mtfurlan/elite-dangerous-control-panel/src/config.cpp

#include "config.h"
bool Config::generateOutput(uint16_t* output, uint16_t button, hid_incoming_data_t* hid)
{
    return false;
}

void Config::setLED(uint16_t* leds, hid_incoming_data_t* hid)
{
    return;
}

int Config::init(void)
{
    return 0;
}
