mtfurlan/elite-dangerous-control-panel/src/config_led.cpp

#include "config_led.h"

void ConfigLED::setLED(uint16_t* leds, hid_incoming_data_t* hid)
{
    if (this->LEDPin) {
        bool input_state = this->GetState(hid);
        CFG_SET_BIT_VAL(*leds, this->LEDPin, input_state);
    }
}
