mtfurlan/elite-dangerous-control-panel/src/led.h

#ifndef LED_H
#define LED_H

#include <mcp23017.h>
#include <stddef.h>

typedef enum {
    BLINK_NOT_OFF = 0,
    BLINK_NOT_MOUNTED = 250,
    BLINK_MOUNTED = 1000,
    BLINK_SUSPENDED = 2500,
} led_state_t;

int led_init(i2c_inst* i2c, uint8_t addr);
int led_task(led_state_t state, uint16_t states);
void led_error();

#endif // LED_H
